bryangalecio04/Aircraft-Telemetry-and-Stabilization/hardware/kicad_files/Aircraft-Telemetry-and-Stabilization.kicad_sch

## KiCad design hardware/kicad_files/Aircraft-Telemetry-and-Stabilization.kicad_sch (2025-08-25)

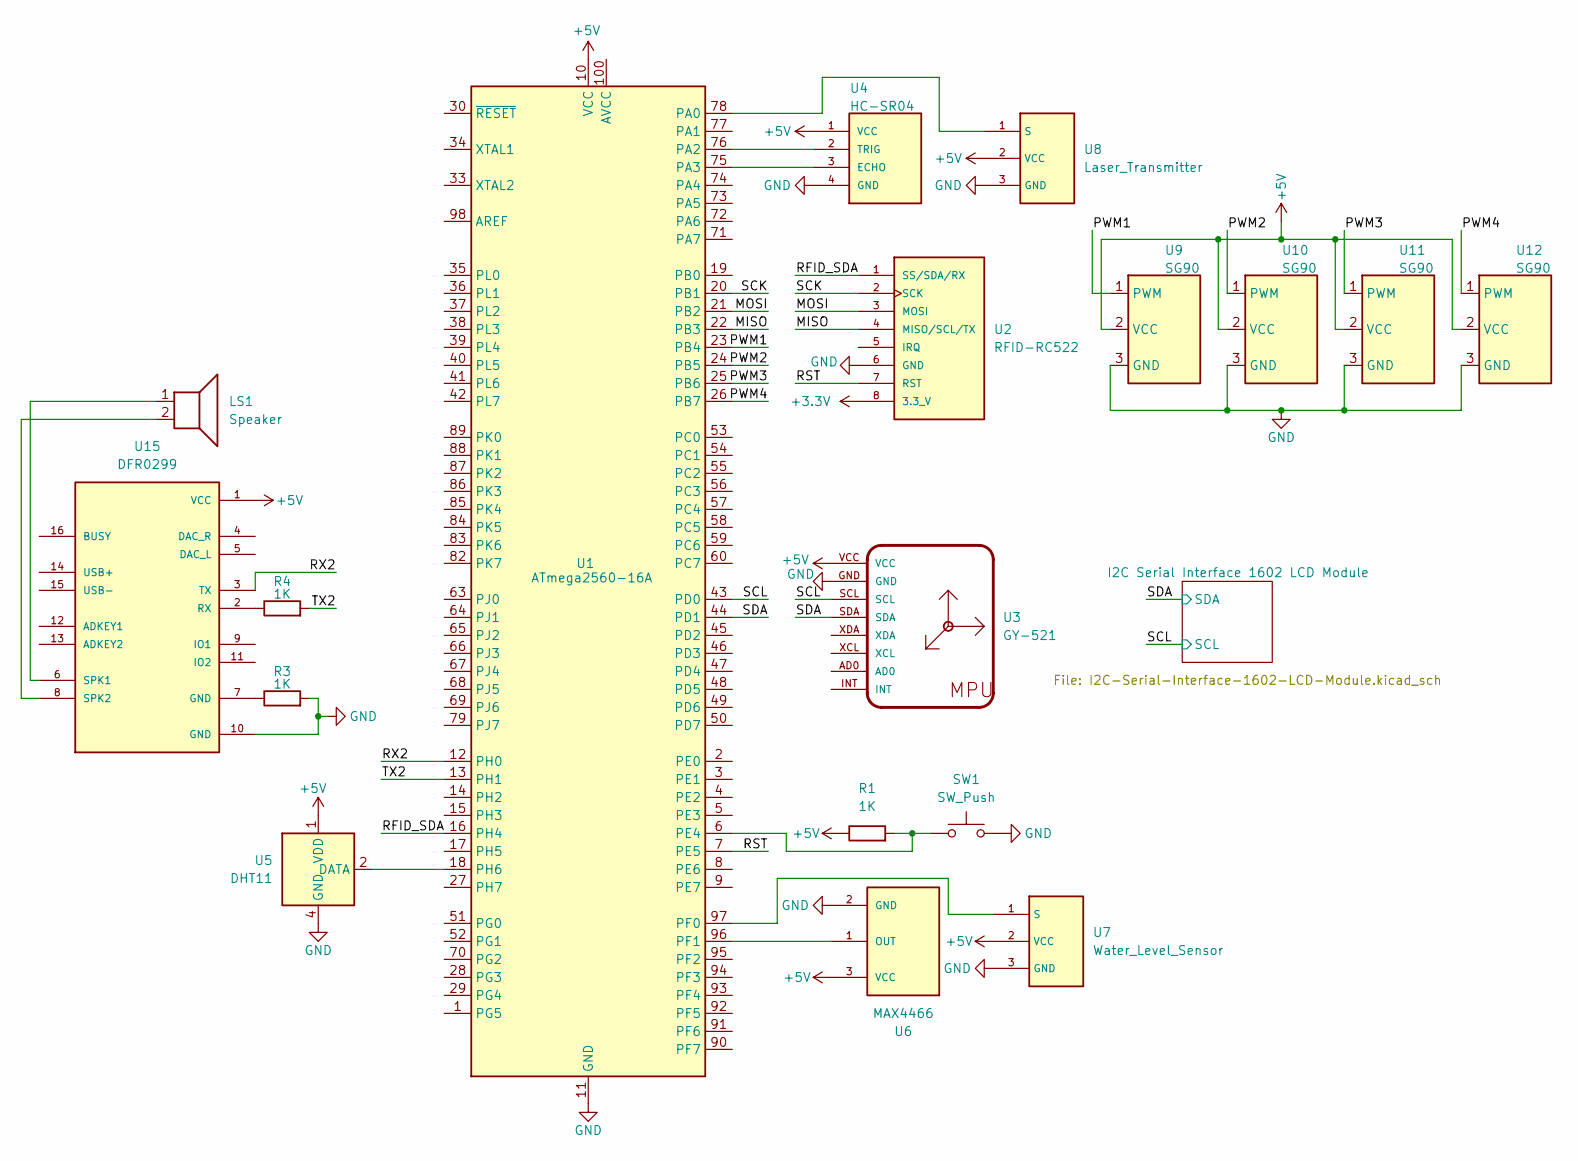
[picture p7: schematic Aircraft-Telemetry-and-Stabilization.kicad_sch]

Parts:
LS1: Speaker
R1, R3, R4: 1K
SW1: SW_Push
U1: ATmega2560-16A; TQFP-100_14x14mm_P0.5mm
U2: RFID-RC522
U3: GY-521
U4: HC-SR04; XCVR_HC-SR04
U5: DHT11; Aosong_DHT11_5.5x12.0_P2.54mm
U6: MAX4466
U7: Water_Level_Sensor
U8: Laser_Transmitter
U9, U10, U11, U12: SG90
U15: DFR0299; MODULE_DFR0299

Connections:
+3.3V: U2.8 (3.3_V)
+5V: R1.1, U1.10 (VCC), U1.31 (VCC), U1.61 (VCC), U1.80 (VCC), U3.VCC, U4.1 (VCC), U5.1 (VDD), U6.3 (VCC), U7.2 (VCC), U8.2 (VCC), U9.2 (VCC), U10.2 (VCC), U11.2 (VCC), U12.2 (VCC), U15.1 (VCC)
GND: R3.2, SW1.2, U1.11 (GND), U1.32 (GND), U1.62 (GND), U1.81 (GND), U1.99 (GND), U2.6 (GND), U3.GND, U4.4 (GND), U5.4 (GND), U6.2 (GND), U7.3 (GND), U8.3 (GND), U9.3 (GND), U10.3 (GND), U11.3 (GND), U12.3 (GND), U15.10 (GND)
MISO: U1.22 (PB3), U2.4 (MISO/SCL/TX)
MOSI: U1.21 (PB2), U2.3 (MOSI)
unnamed: LS1.1, U15.6 (SPK1)
unnamed: LS1.2, U15.8 (SPK2)
unnamed: R1.2, SW1.1, U1.6 (PE4)
unnamed: R3.1, U15.7 (GND)
unnamed: R4.1, U15.2 (RX)
unnamed: U1.18 (PH6), U5.2 (DATA)
unnamed: U1.75 (PA3), U4.3 (ECHO)
unnamed: U1.76 (PA2), U4.2 (TRIG)
unnamed: U1.78 (PA0), U8.1 (S)
unnamed: U1.96 (PF1), U6.1 (OUT)
unnamed: U1.97 (PF0), U7.1 (S)
PWM1: U1.23 (PB4), U9.1 (PWM)
PWM2: U1.24 (PB5), U10.1 (PWM)
PWM3: U1.25 (PB6), U11.1 (PWM)
PWM4: U1.26 (PB7), U12.1 (PWM)
RFID_SDA: U1.16 (PH4), U2.1 (SS/SDA/RX)
RST: U1.7 (PE5), U2.7 (RST)
RX2: U1.12 (PH0), U15.3 (TX)
SCK: U1.20 (PB1), U2.2 (SCK)
SCL: U1.43 (PD0), U3.SCL
SDA: U1.44 (PD1), U3.SDA
TX2: R4.2, U1.13 (PH1)
