bryangalecio04/Aircraft-Telemetry-and-Stabilization/hardware/kicad_files/I2C-Serial-Interface-1602-LCD-Module.kicad_sch

## KiCad design hardware/kicad_files/I2C-Serial-Interface-1602-LCD-Module.kicad_sch (2025-08-25)

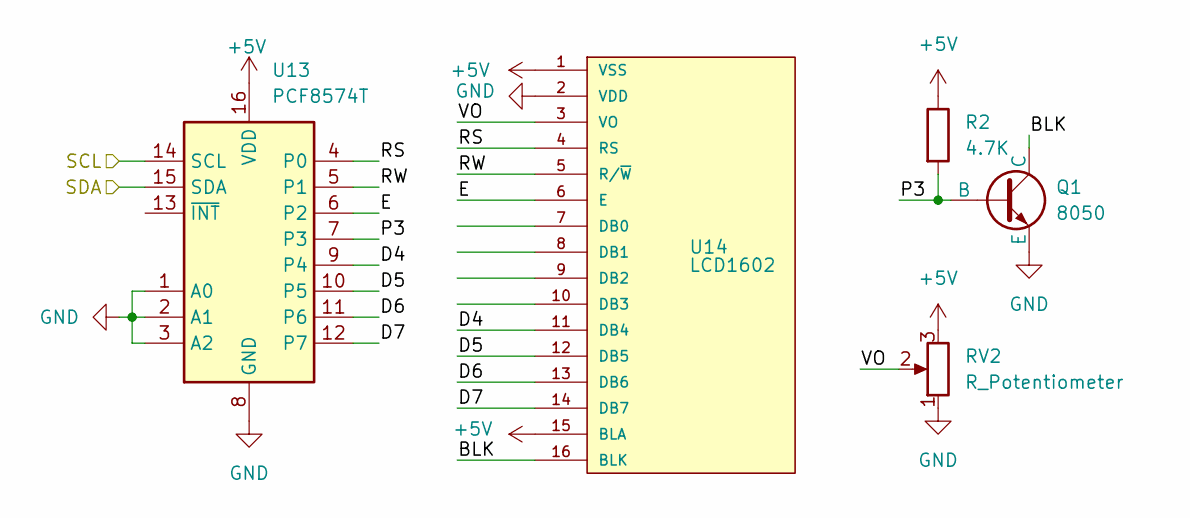
[picture p8: schematic I2C-Serial-Interface-1602-LCD-Module.kicad_sch]

Parts:
Q1: 8050; TO-92_Inline
R2: 4.7K
RV2: R_Potentiometer
U13: PCF8574T; SOIC-16W_7.5x10.3mm_P1.27mm
U14: LCD1602; LCD_RC1602B-BIW-CSV

Connections:
+5V: R2.1, RV2.3, U13.16 (VDD), U14.1 (VSS), U14.15 (BLA)
BLK: Q1.3 (C), U14.16 (BLK)
D4: U13.9 (P4), U14.11 (DB4)
D5: U13.10 (P5), U14.12 (DB5)
D6: U13.11 (P6), U14.13 (DB6)
D7: U13.12 (P7), U14.14 (DB7)
E: U13.6 (P2), U14.6 (E)
GND: Q1.1 (E), RV2.1, U13.1 (A0), U13.2 (A1), U13.3 (A2), U13.8 (GND), U14.2 (VDD)
P3: Q1.2 (B), R2.2, U13.7 (P3)
RS: U13.4 (P0), U14.4 (RS)
RW: U13.5 (P1), U14.5 (R/~W)
SCL: U13.14 (SCL)
SDA: U13.15 (SDA)
VO: RV2.2, U14.3 (VO)
